fpeyraud/ihm_light/arduino_code/IHM_light/led_scroll.h

#define SCROLL_STATE_MAX 12
const char scroll[SCROLL_STATE_MAX][4] = {
                            {'R','0','0','0'},
                            {'0','R','0','0'},
                            {'0','0','R','0'},
                            {'0','0','0','O'},
                            {'0','0','G','0'},
                            {'0','G','0','0'},
                            {'C','0','0','0'},
                            {'0','B','0','0'},
                            {'0','0','B','0'},
                            {'0','0','0','P'},
                            {'0','0','R','0'},
                            {'0','R','0','0'},
                           };
